palto42/komoot-navi/navi-case/navi-case-plug.png

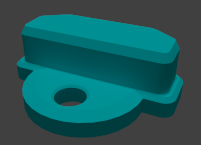
navi-case/navi-case-plug.png
